reykato/voicerobots/Assignments/Assignment 3 Design Review/Sequence_Diagram_2.png

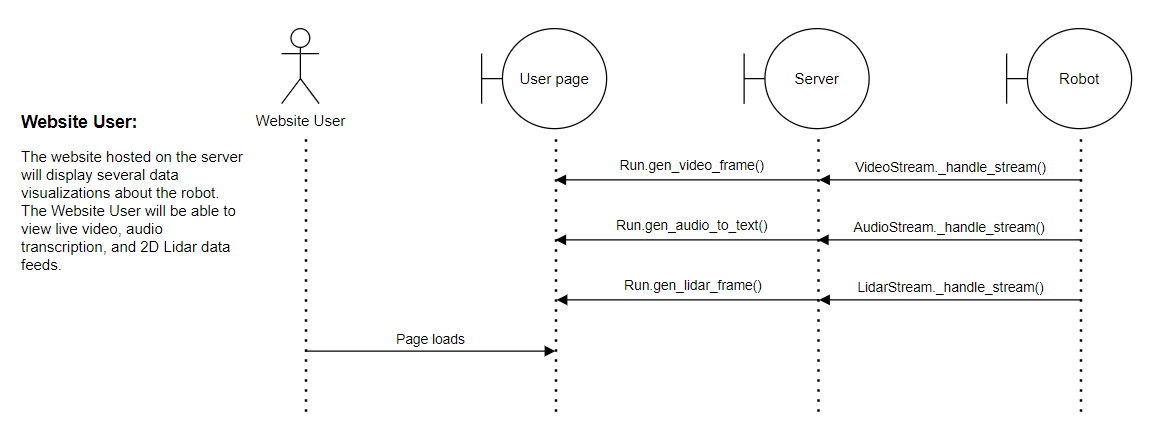
Assignments/Assignment 3 Design Review/Sequence_Diagram_2.png
