reykato/voicerobots/images/lidar.png

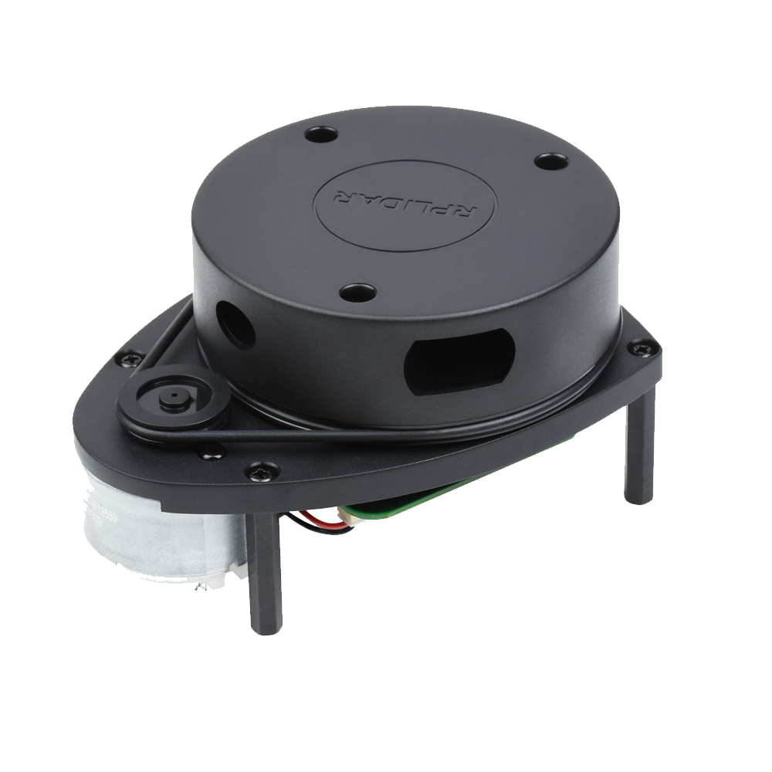
images/lidar.png
