reykato/voicerobots/images/motor.png

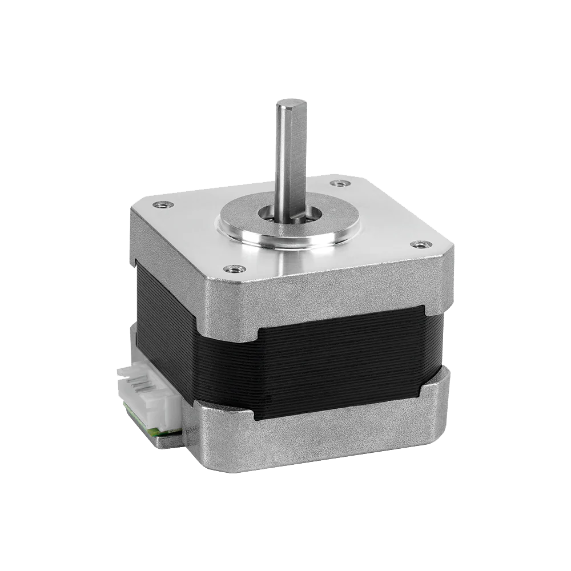
images/motor.png
