reykato/voicerobots/images/renders/robot1.JPG

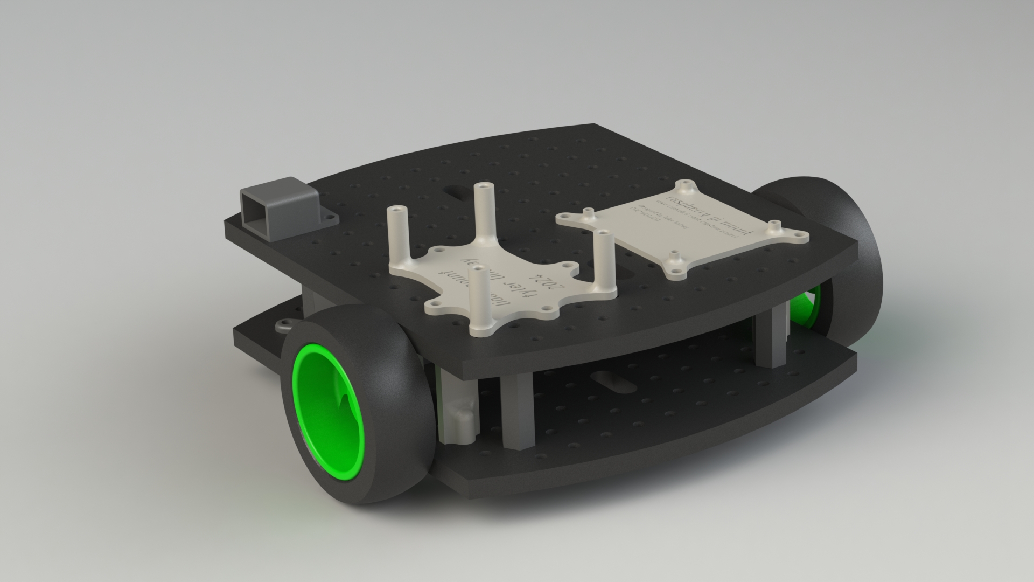
images/renders/robot1.JPG
