reykato/voicerobots/images/renders/robot2.JPG

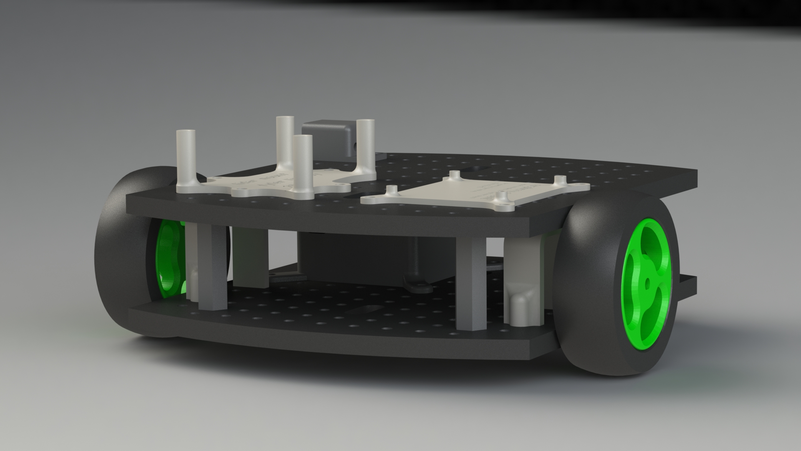
images/renders/robot2.JPG
