reykato/voicerobots/images/renders/robot3.JPG

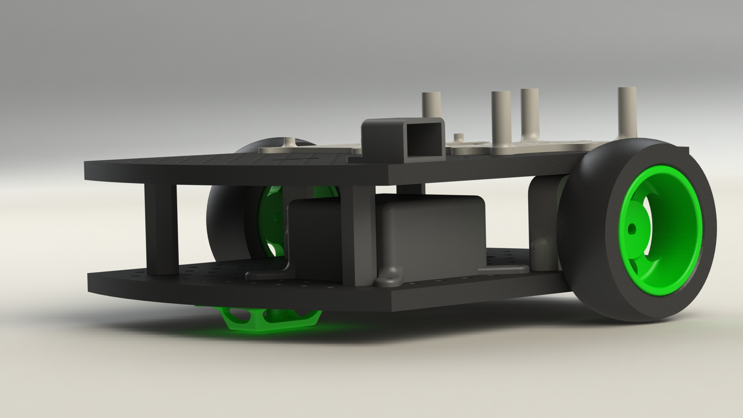
images/renders/robot3.JPG
