reykato/voicerobots/images/robot/20240418_105205.jpg

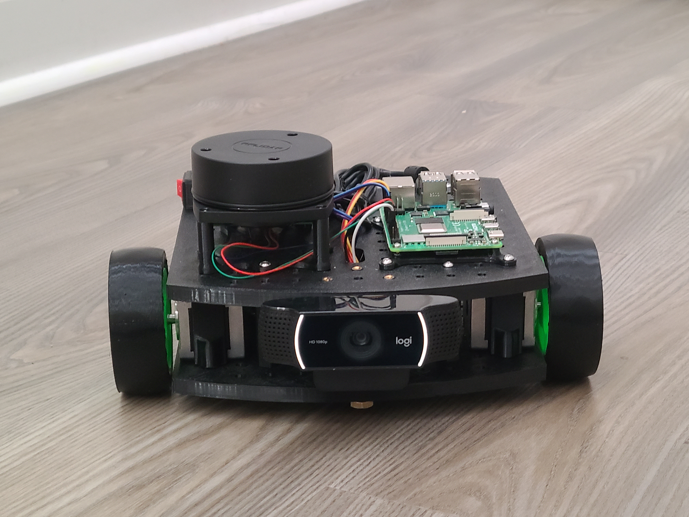
images/robot/20240418_105205.jpg
