reykato/voicerobots/images/robot/20240418_105216.jpg

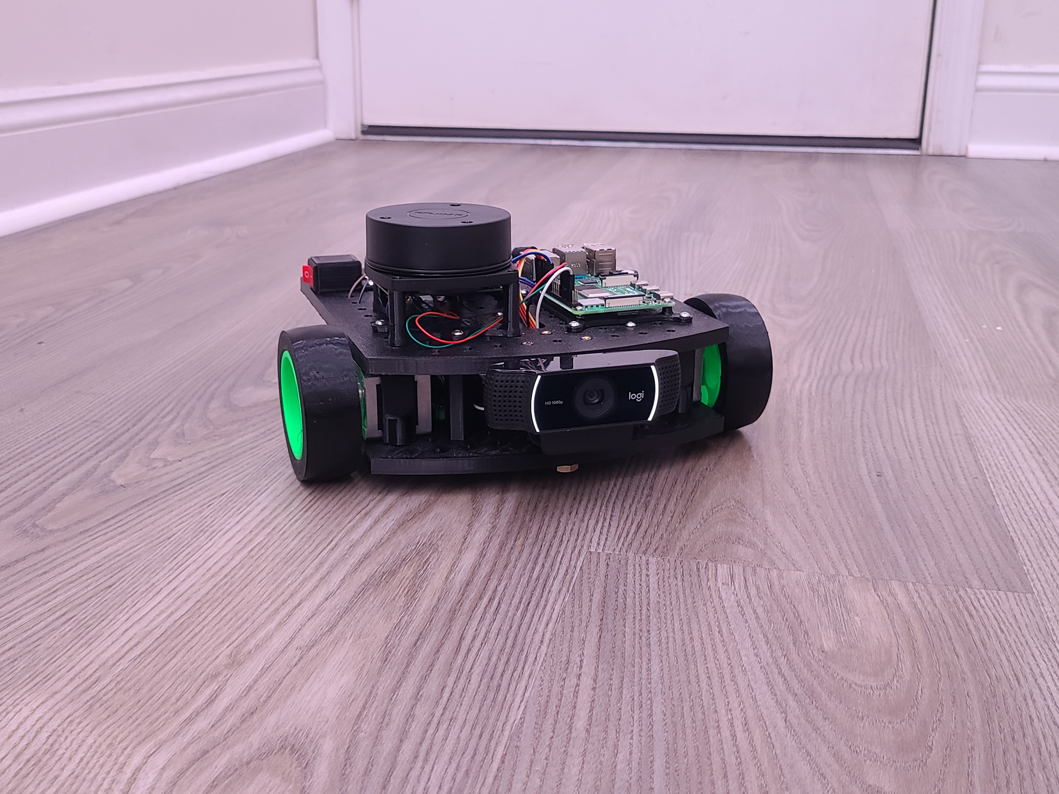
images/robot/20240418_105216.jpg
