reykato/voicerobots/images/robot/20240418_105219.jpg

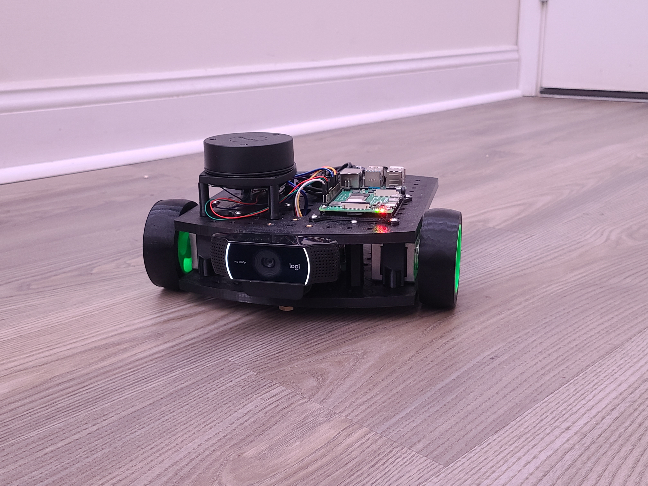
images/robot/20240418_105219.jpg
