reykato/voicerobots/images/robot/20240418_105221.jpg

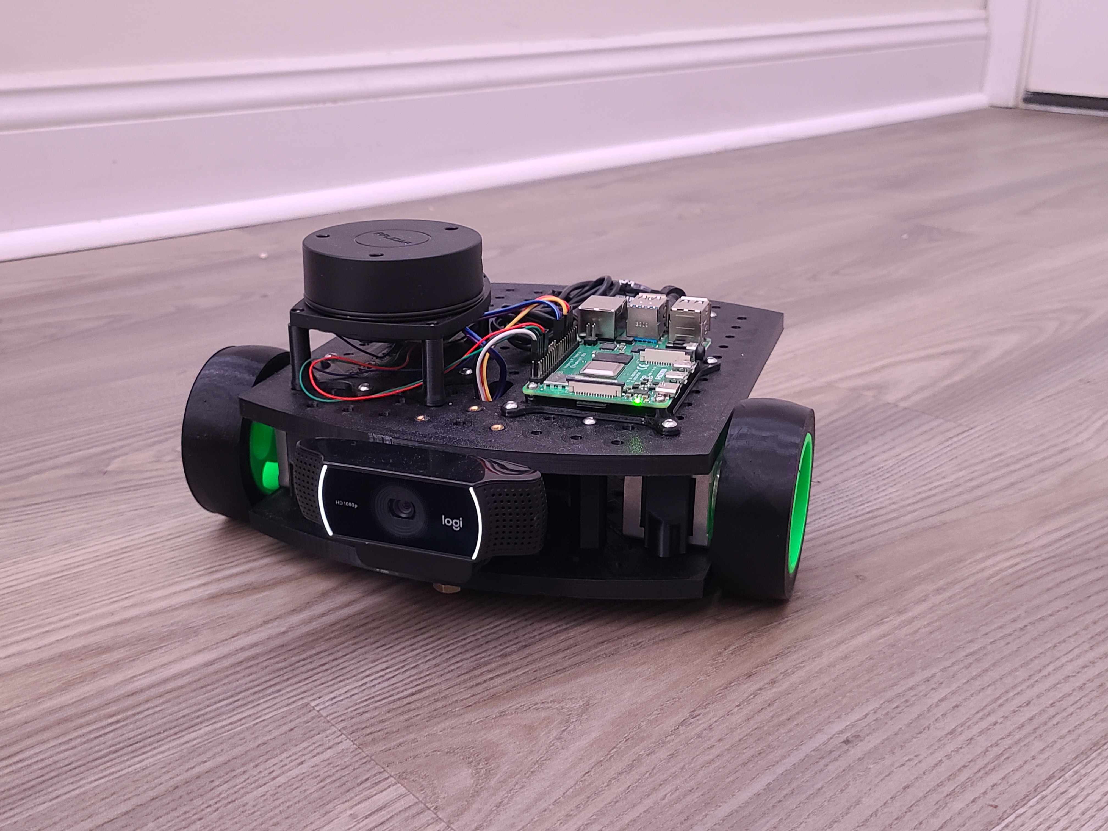
images/robot/20240418_105221.jpg
