reykato/voicerobots/images/robot/20240418_105225.jpg

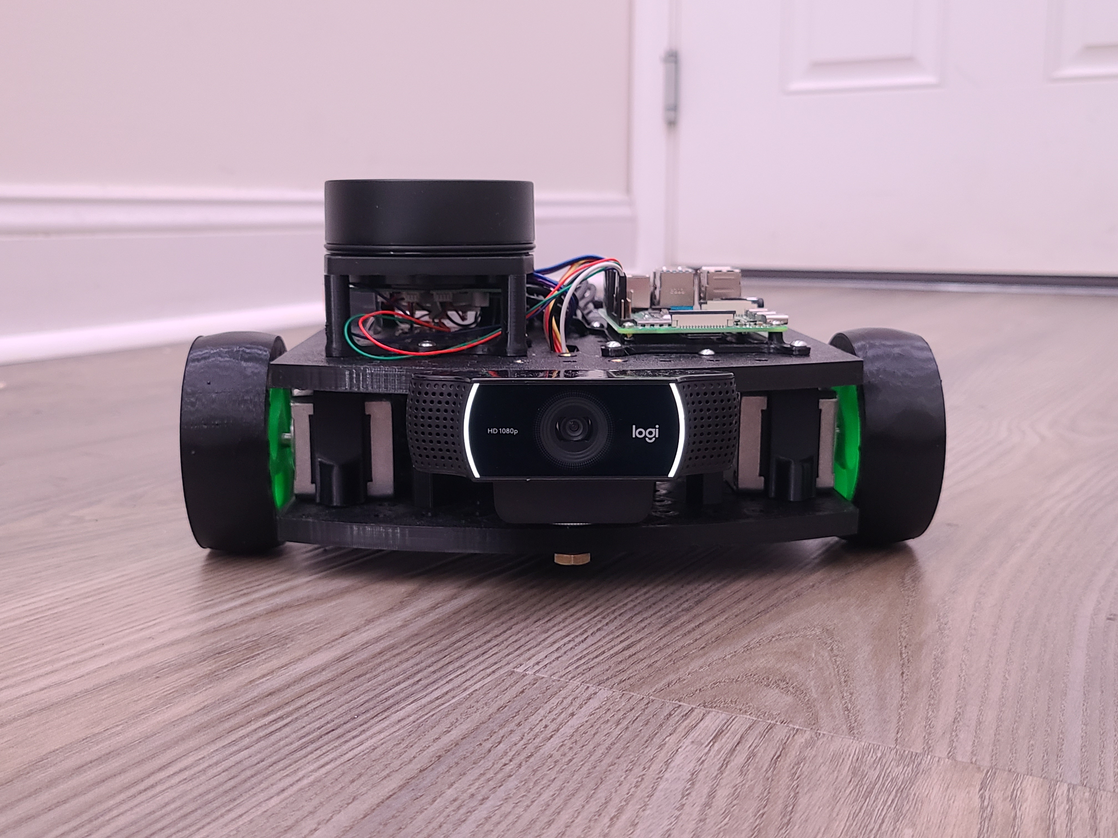
images/robot/20240418_105225.jpg
