reykato/voicerobots/images/robot/20240418_105230.jpg

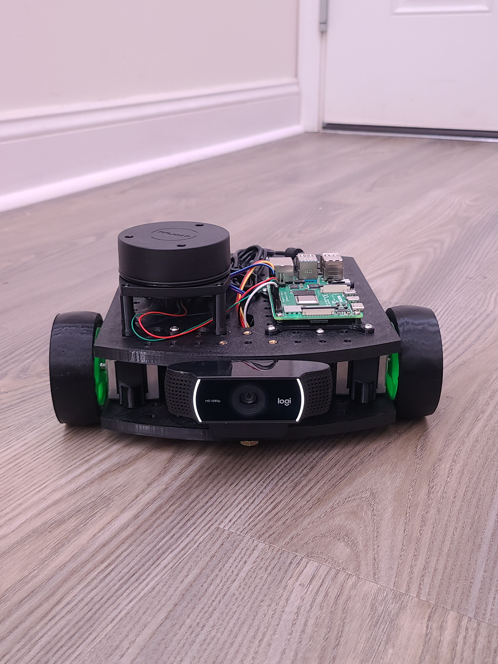
images/robot/20240418_105230.jpg
