reykato/voicerobots/images/robot/20240418_110318.jpg

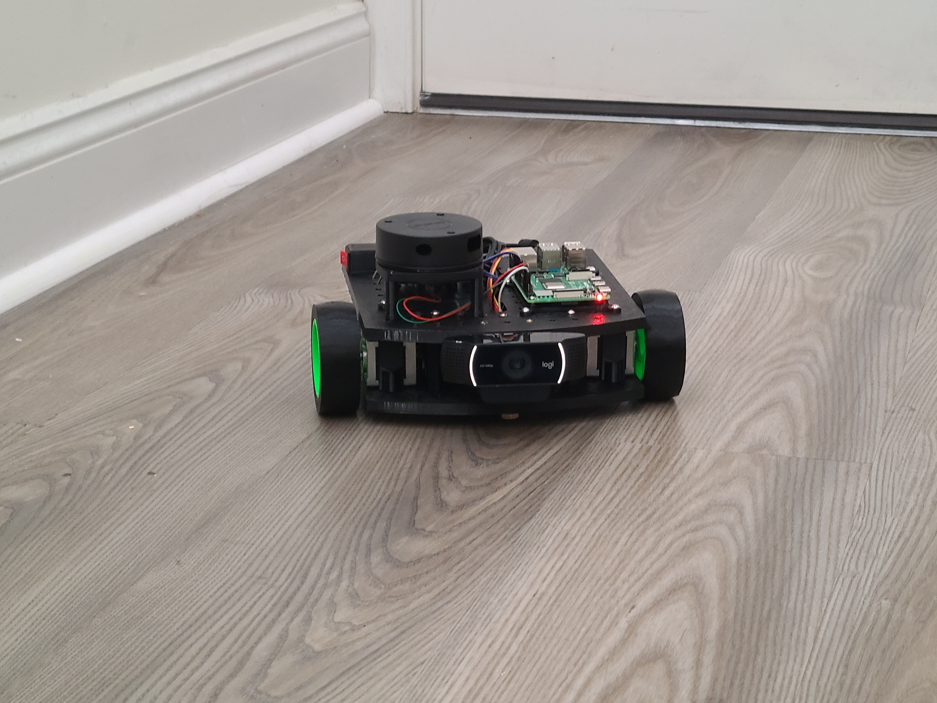
images/robot/20240418_110318.jpg
