reykato/voicerobots/images/robot/20240418_110321.jpg

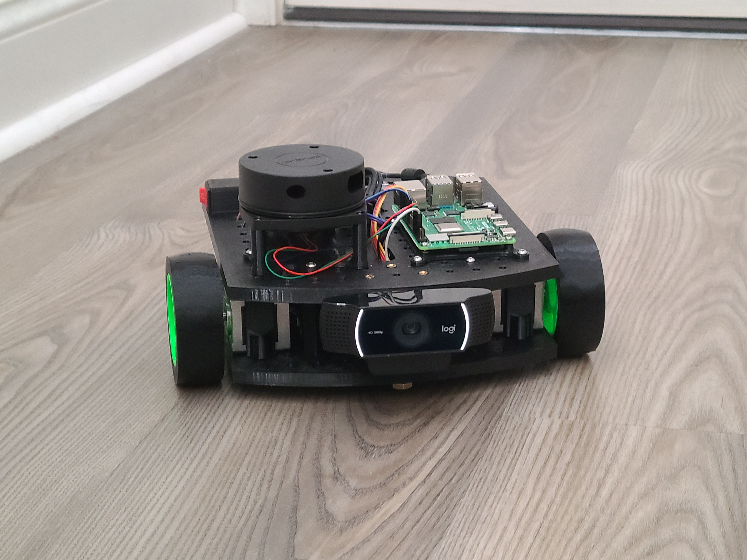
images/robot/20240418_110321.jpg
