reykato/voicerobots/images/robot/20240418_110328.jpg

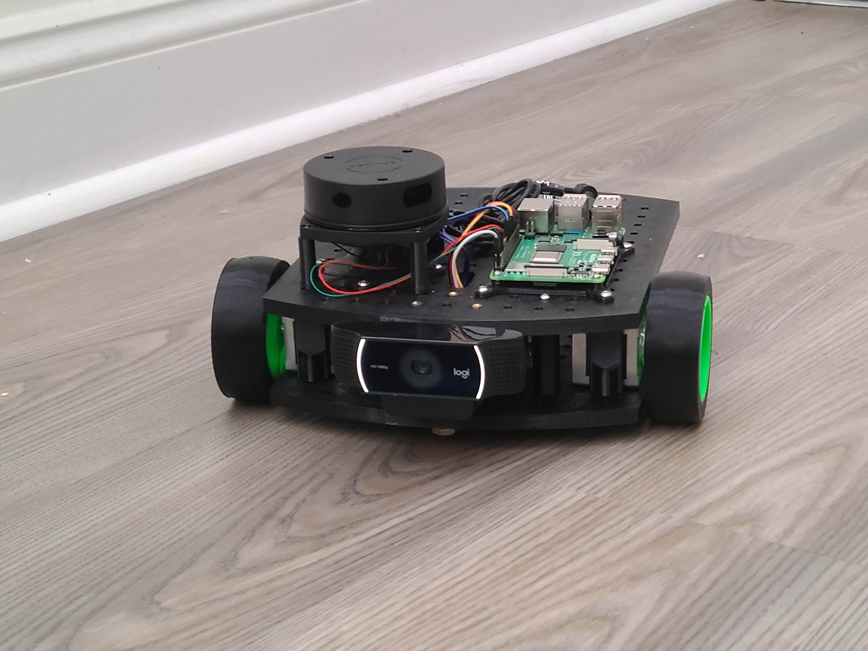
images/robot/20240418_110328.jpg
