reykato/voicerobots/images/stepper_driver.png

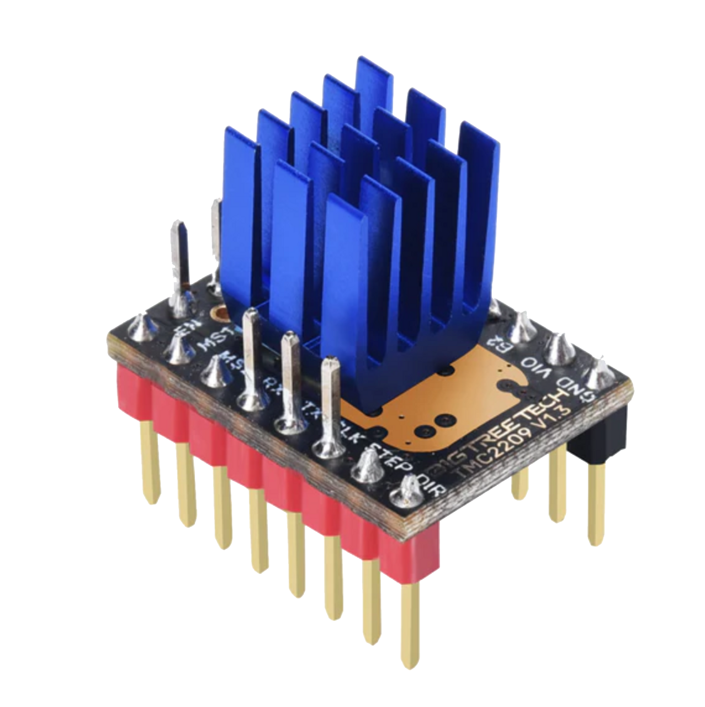
images/stepper_driver.png
