reykato/voicerobots/images/stepper_driver_board_1.png

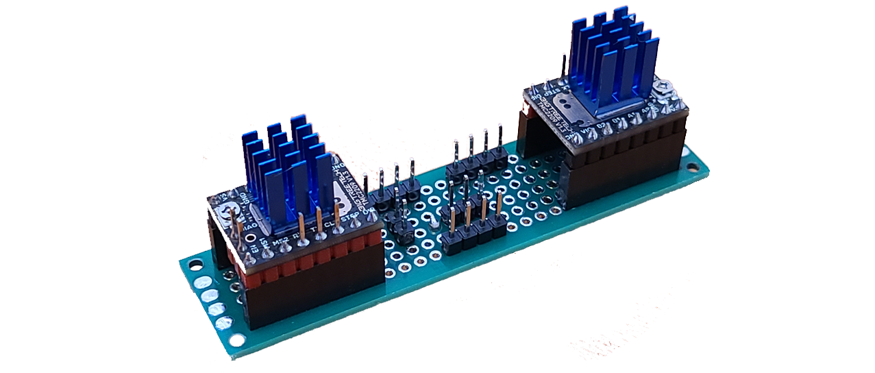
images/stepper_driver_board_1.png
