reykato/voicerobots/images/webcam.png

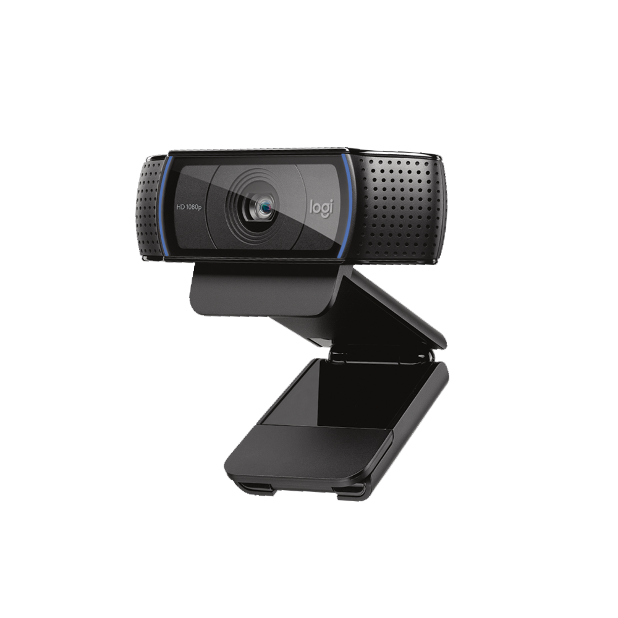
images/webcam.png
