reykato/voicerobots/models/Robot_Frame_RevA.SLDPRT

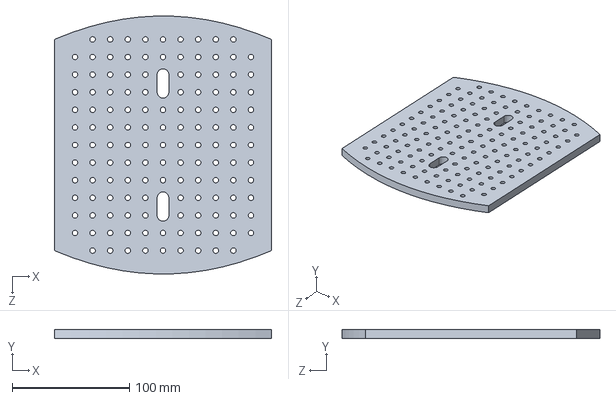
[picture p43: CAD file, 2024-01-22]
models/Robot_Frame_RevA.SLDPRT
185.0 x 8.00 x 219.8 mm
