reykato/voicerobots/models/Battery_Pack_Box_RevA.SLDPRT

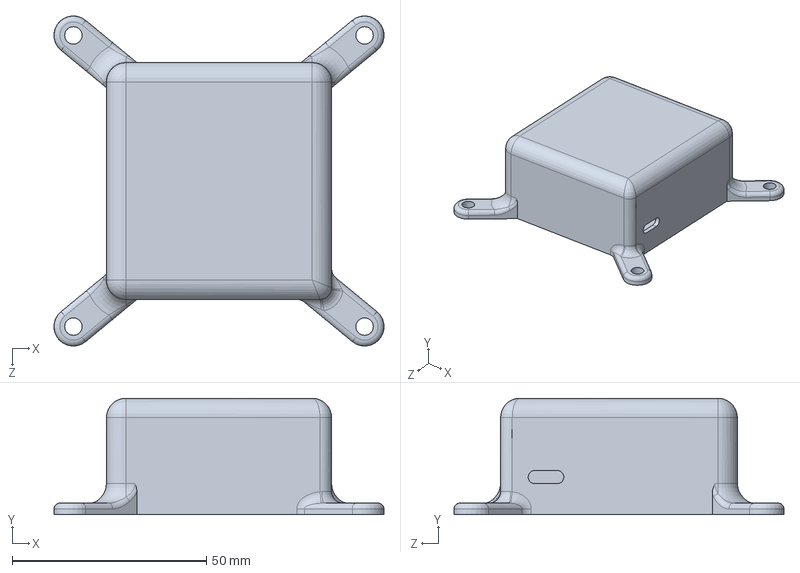
[picture p44: CAD file, 2024-01-22]
models/Battery_Pack_Box_RevA.SLDPRT
85.0 x 30.0 x 85.0 mm
