reykato/voicerobots/models/Raspberry_Pi_Mount_RevA.SLDPRT

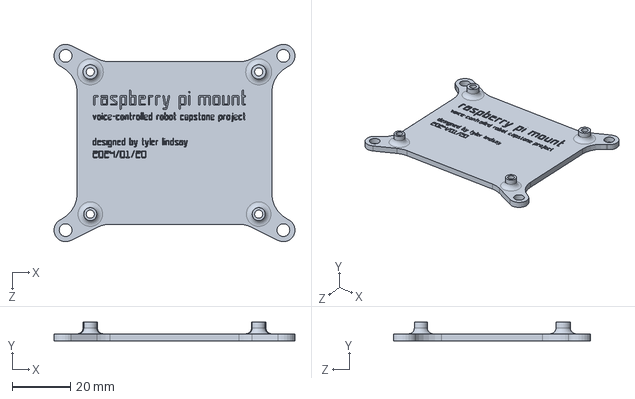
[picture p45: CAD file, 2024-01-22]
models/Raspberry_Pi_Mount_RevA.SLDPRT
83.0 x 6.40 x 68.0 mm
