reykato/voicerobots/models/05mm_Riser_RevA.STL

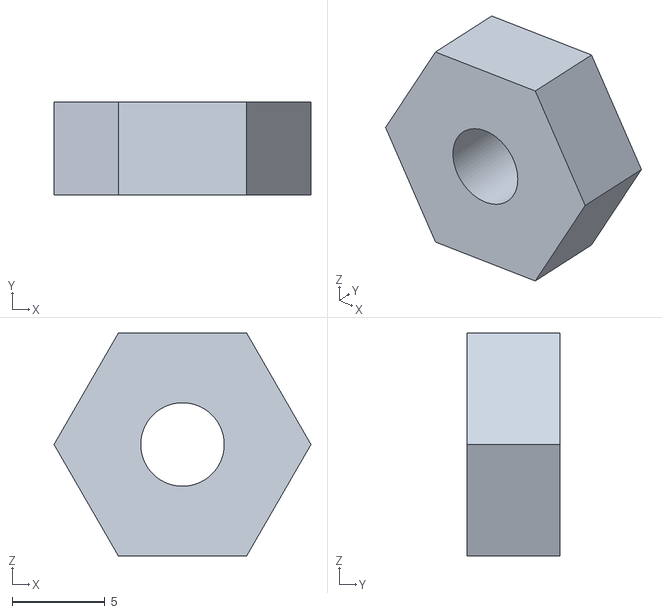
[picture p46: CAD file, 2024-01-22]
models/05mm_Riser_RevA.STL
13.9 x 5.00 x 12.0
