reykato/voicerobots/images/robot/20240418_105200.jpg

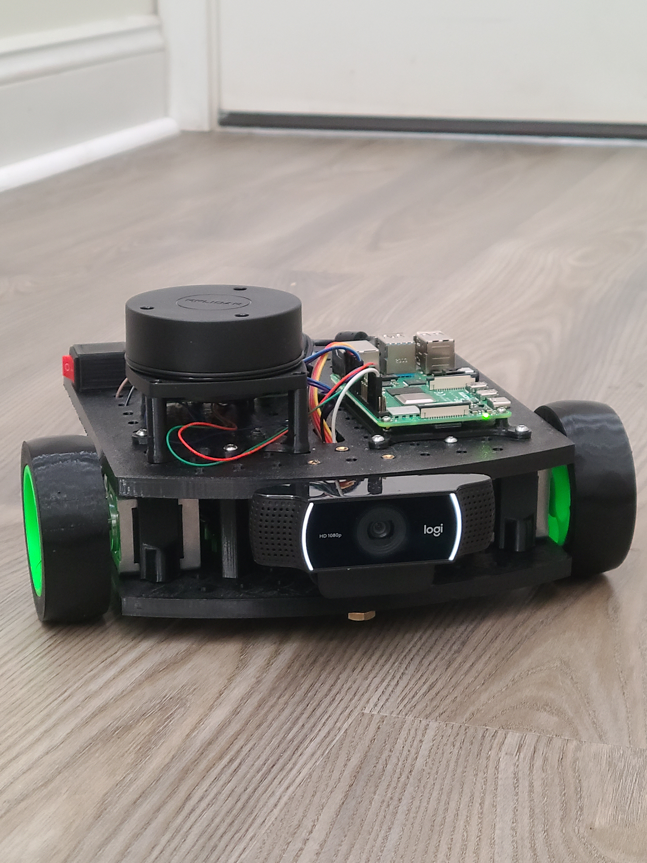
images/robot/20240418_105200.jpg
